JeffRocchio/Wireless-Soil-Moisture-Sensor/Software/tiny84/tiny84_SensorAsSlave/TC03_TransmitPOC/TC03_TransmitPOC_terminalDisplay.jpg

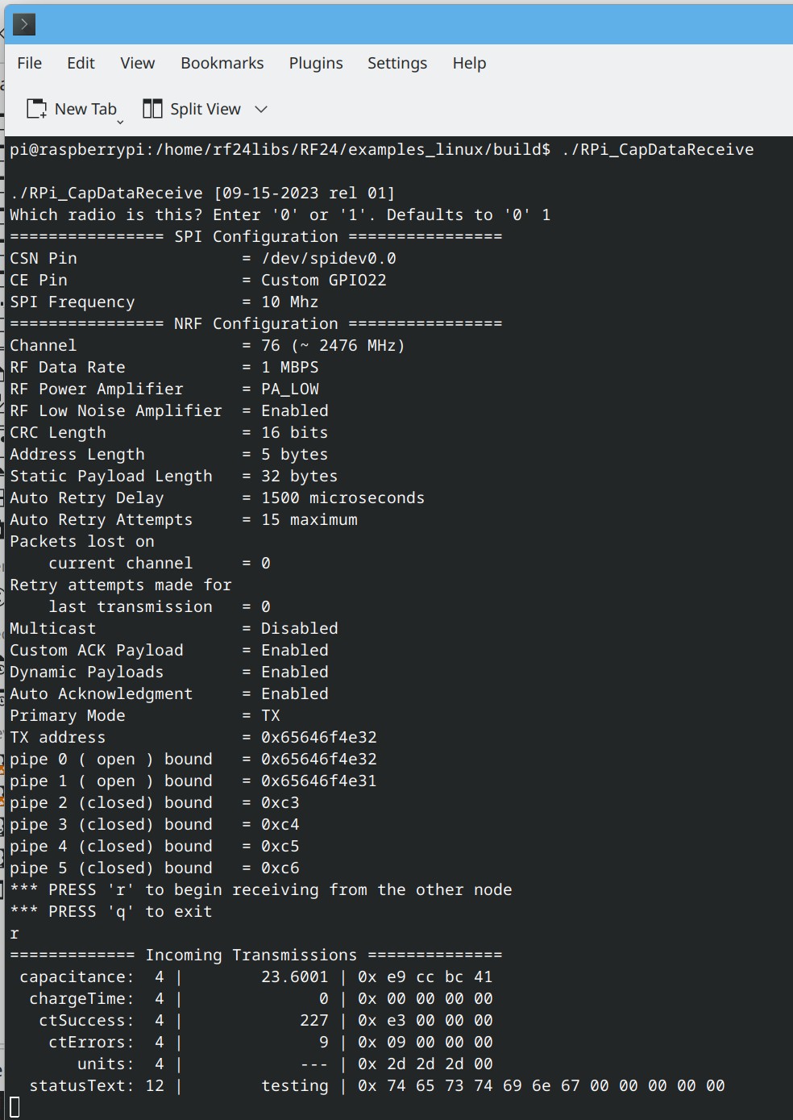
Software/tiny84/tiny84_SensorAsSlave/TC03_TransmitPOC/TC03_TransmitPOC_terminalDisplay.jpg
