JeffRocchio/Wireless-Soil-Moisture-Sensor/ProjectLog/MS07_b_Breadboard.jpg

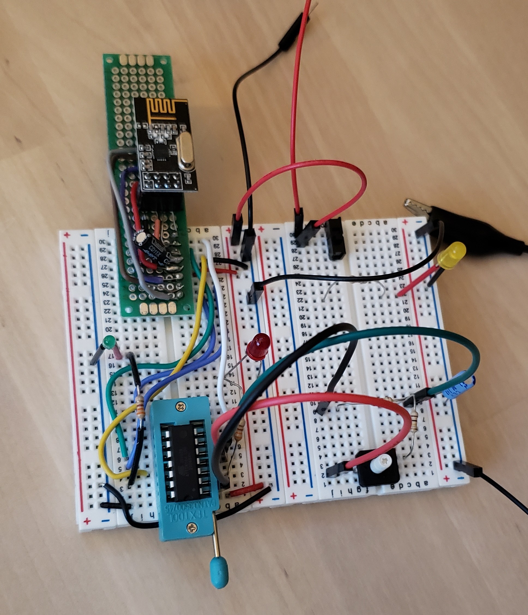
ProjectLog/MS07_b_Breadboard.jpg
