JeffRocchio/Wireless-Soil-Moisture-Sensor/ProjectLog/MS07_c_Success_RPi-console-output.png

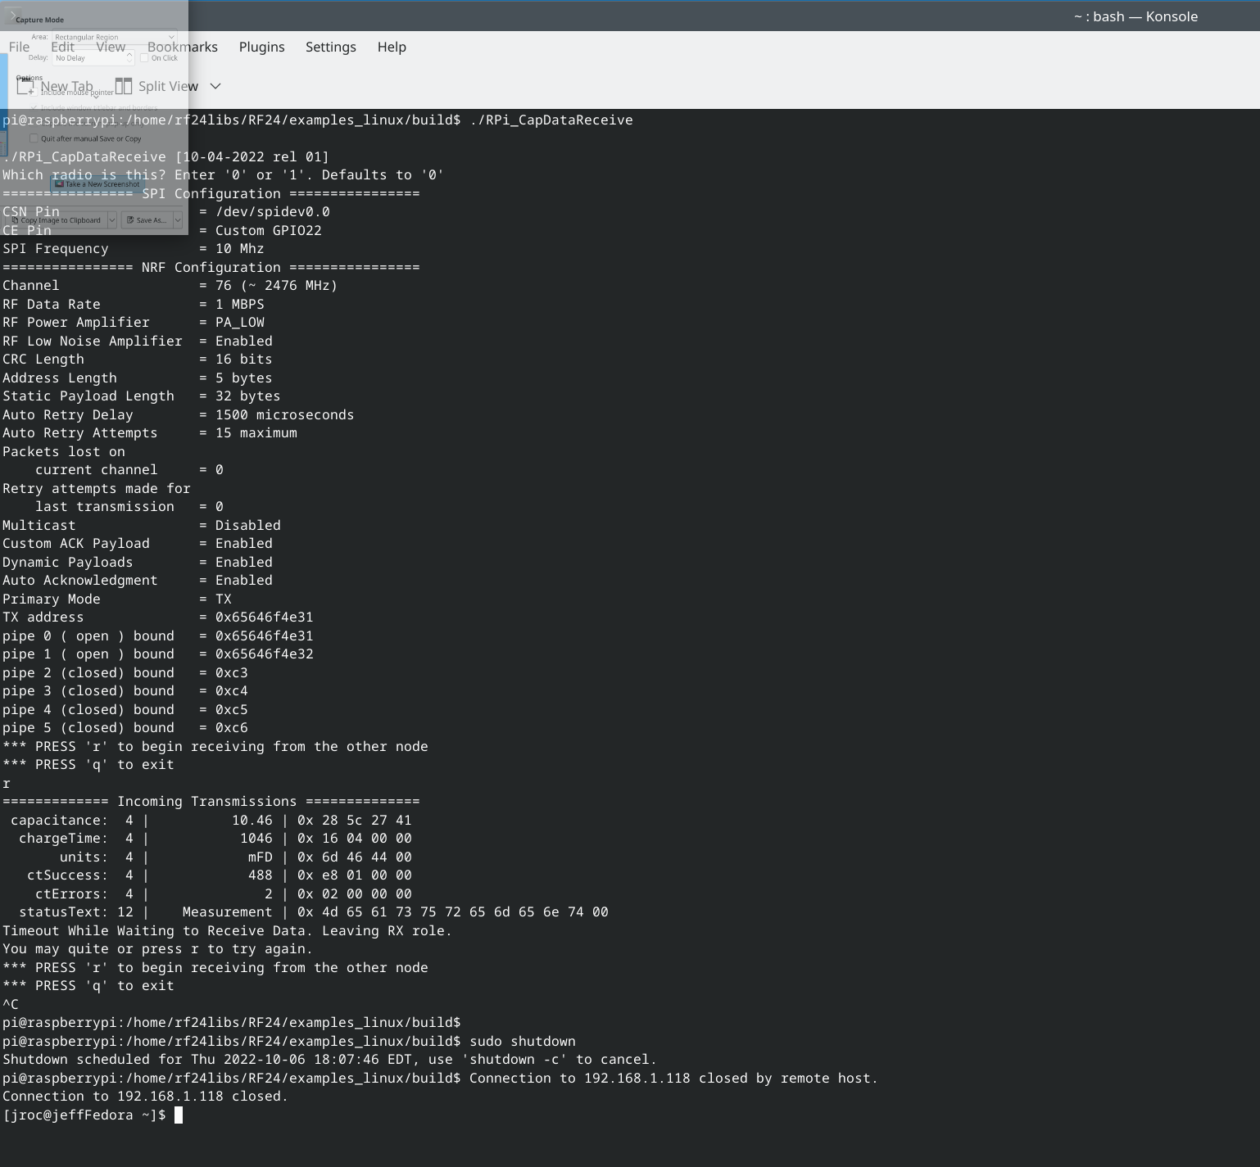
ProjectLog/MS07_c_Success_RPi-console-output.png
