JeffRocchio/Wireless-Soil-Moisture-Sensor/ProjectLog/MS09_c_Sensor-readings.jpg

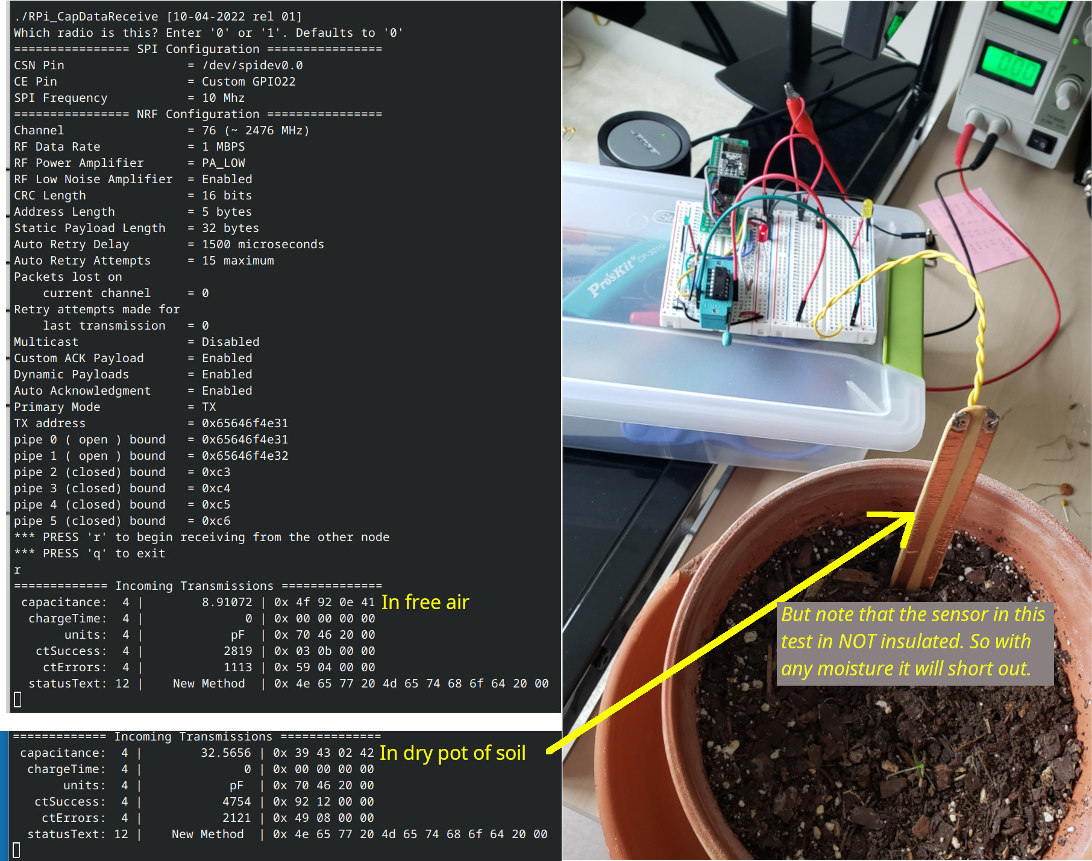
ProjectLog/MS09_c_Sensor-readings.jpg
