JeffRocchio/Wireless-Soil-Moisture-Sensor/ProjectLog/MS10_c_Sensor-readings.jpg

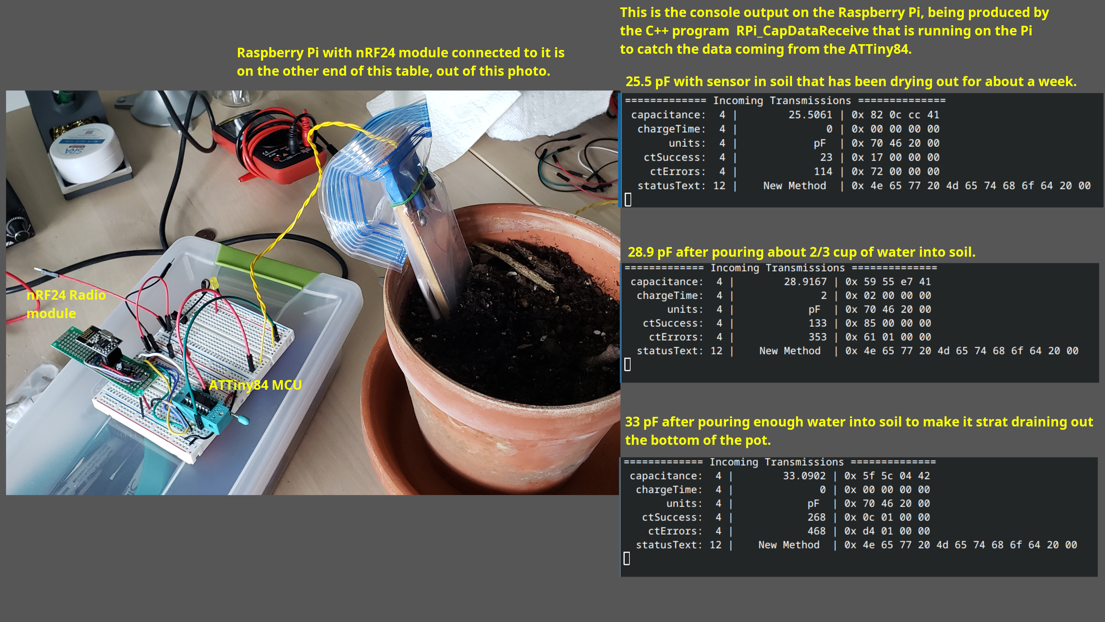
ProjectLog/MS10_c_Sensor-readings.jpg
