JeffRocchio/Wireless-Soil-Moisture-Sensor/ProjectLog/MS11_b_Sensor-on-Perf-Board.jpg

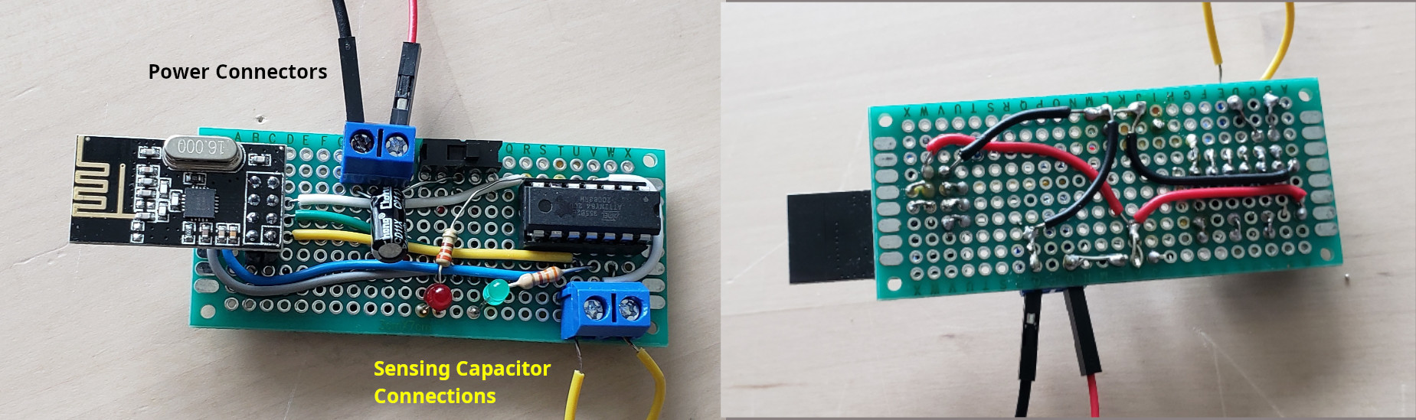
ProjectLog/MS11_b_Sensor-on-Perf-Board.jpg
