JeffRocchio/Wireless-Soil-Moisture-Sensor/ProjectLog/MS11_b_Sensor-on-Perf-Board_WireDiagram.jpg

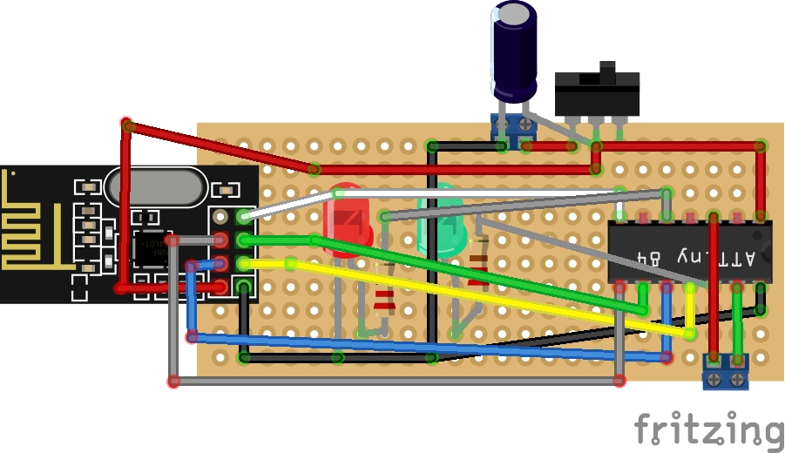
ProjectLog/MS11_b_Sensor-on-Perf-Board_WireDiagram.jpg
